Taro-Hayashi/On-the-15/acrylic-case/fully-acrylic/img/IMG_9139.jpeg

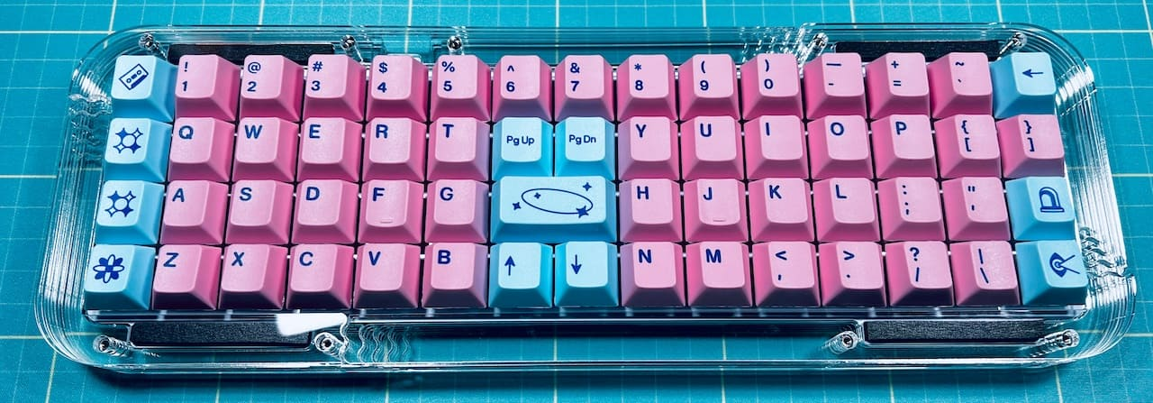
acrylic-case/fully-acrylic/img/IMG_9139.jpeg
