Taro-Hayashi/On-the-15/acrylic-case/fully-acrylic/img/onthe15c.jpg

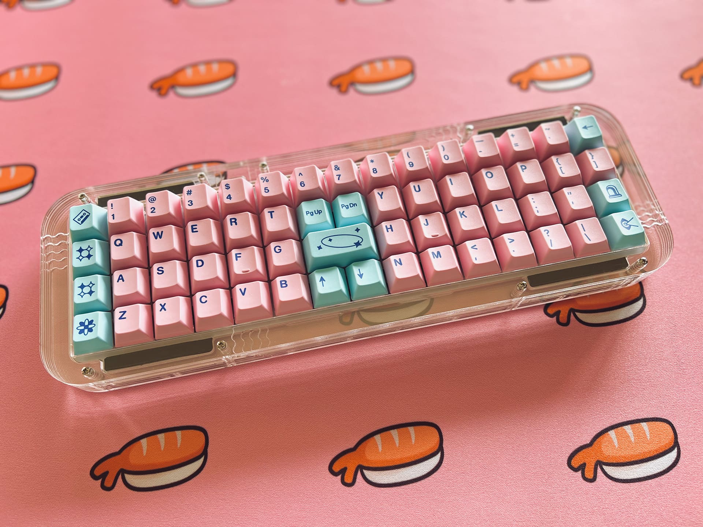
acrylic-case/fully-acrylic/img/onthe15c.jpg
