Taro-Hayashi/On-the-15/img/case1.png

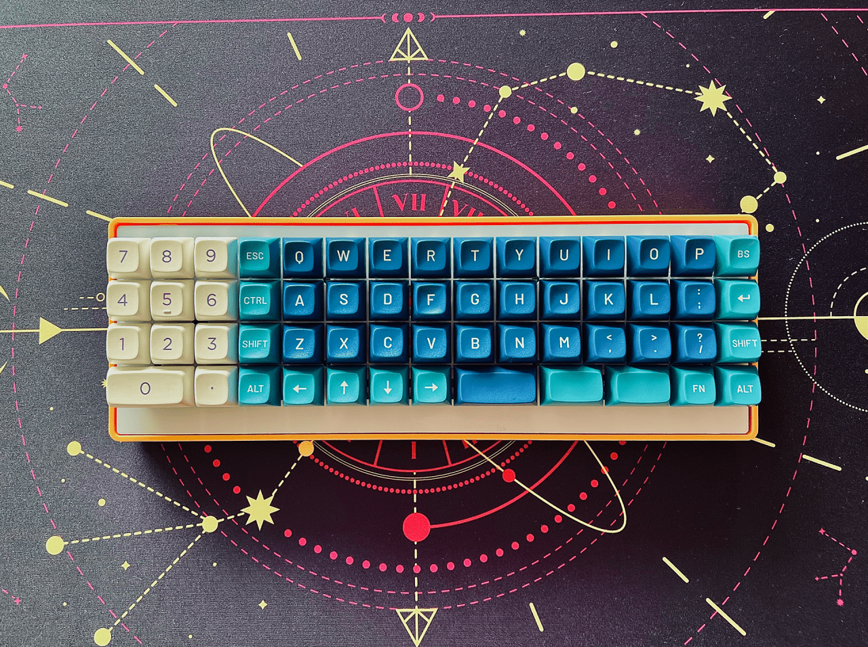
img/case1.png
