Taro-Hayashi/On-the-15/img/case2.png

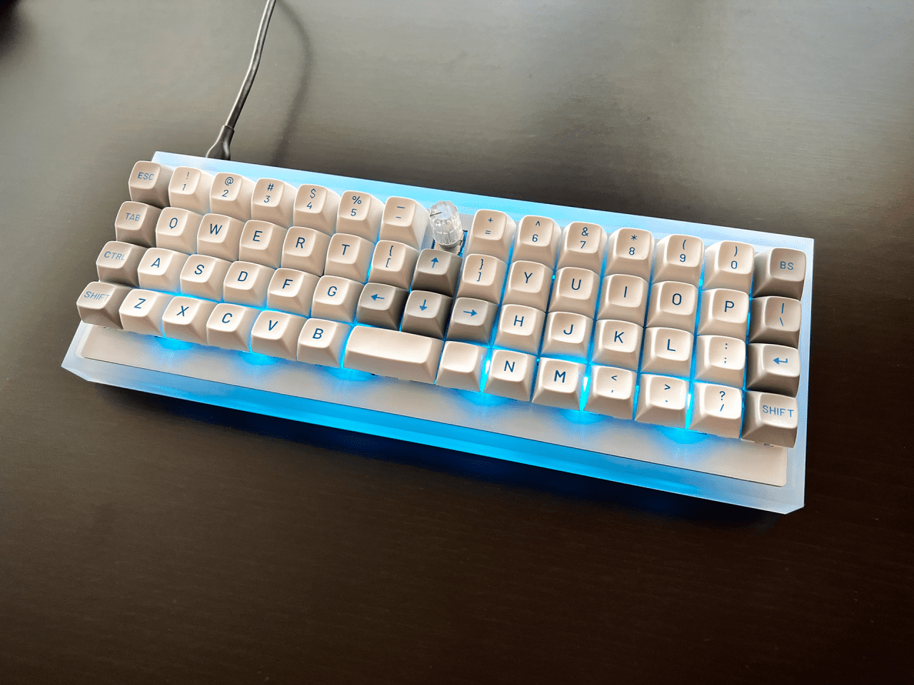
img/case2.png
