Taro-Hayashi/On-the-15/img/IMG_6119.jpg

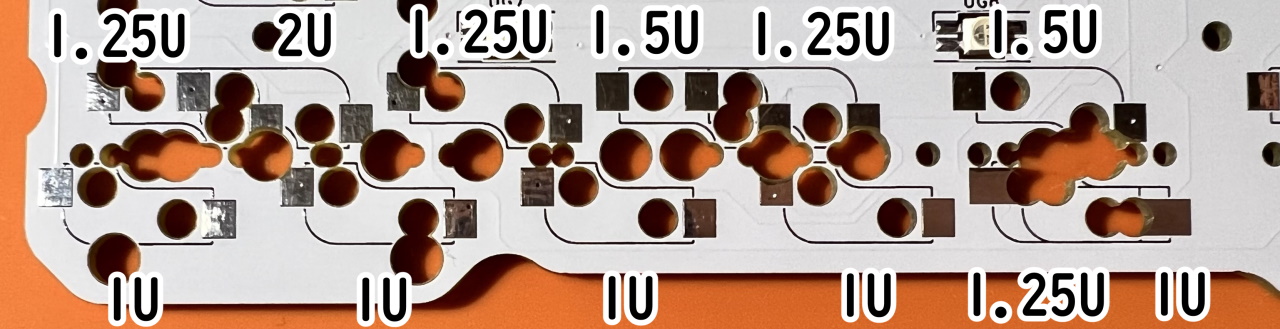
img/IMG_6119.jpg
