Taro-Hayashi/On-the-15/img/IMG_6120.jpg

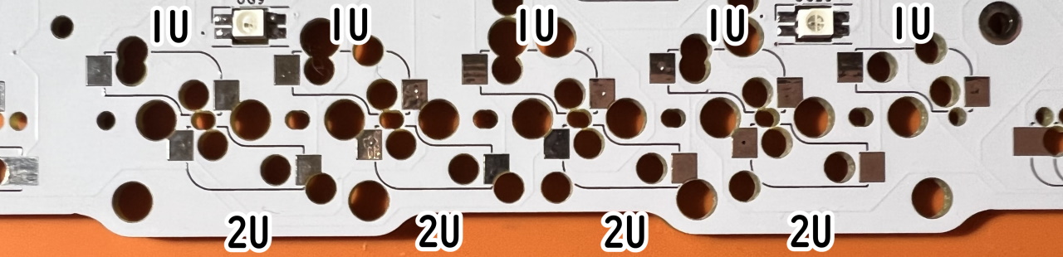
img/IMG_6120.jpg
