Taro-Hayashi/On-the-15/img/IMG_6123.jpg

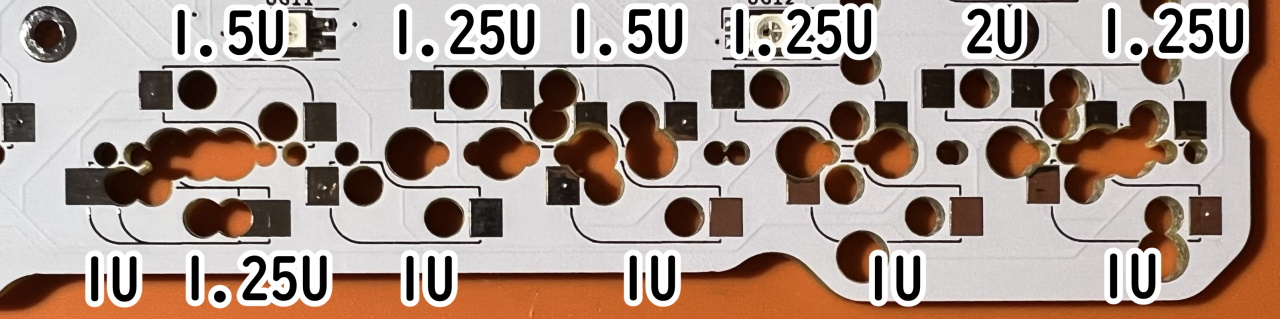
img/IMG_6123.jpg
