Taro-Hayashi/On-the-15/img/IMG_6135.JPEG

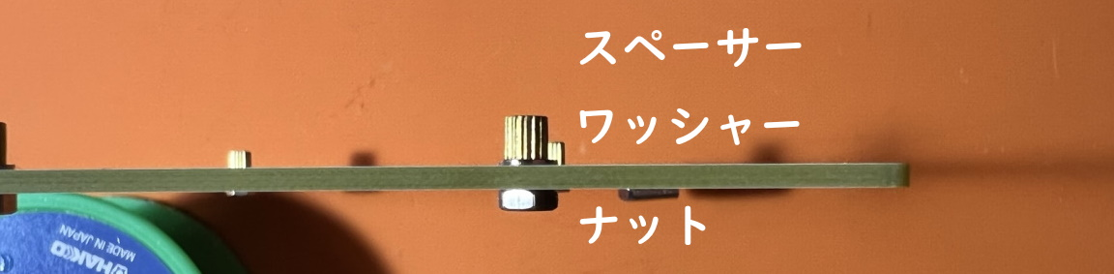
img/IMG_6135.JPEG
