Taro-Hayashi/On-the-15/img/IMG_6159.JPEG

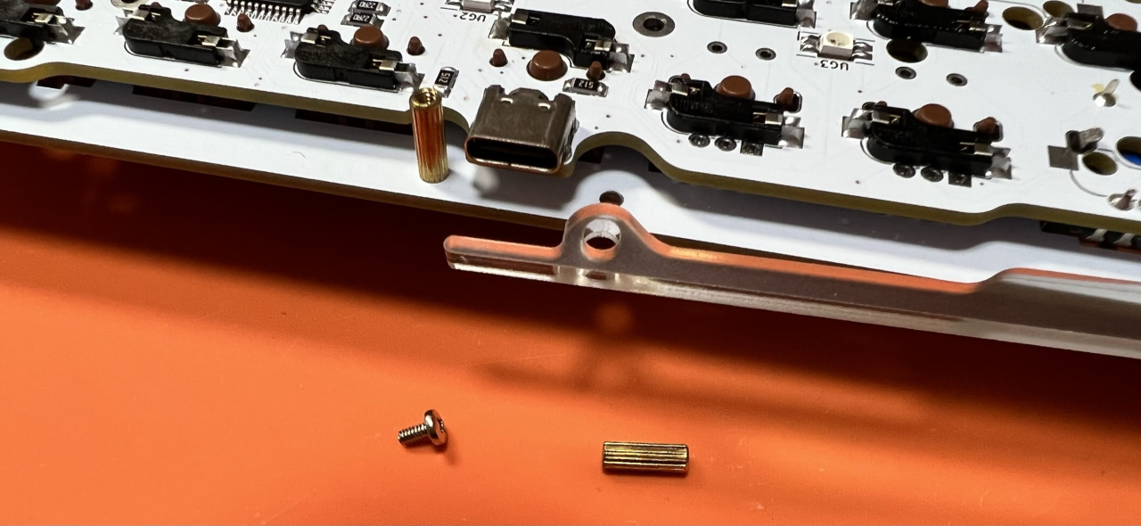
img/IMG_6159.JPEG
