Taro-Hayashi/On-the-15/img/IMG_6162.JPEG

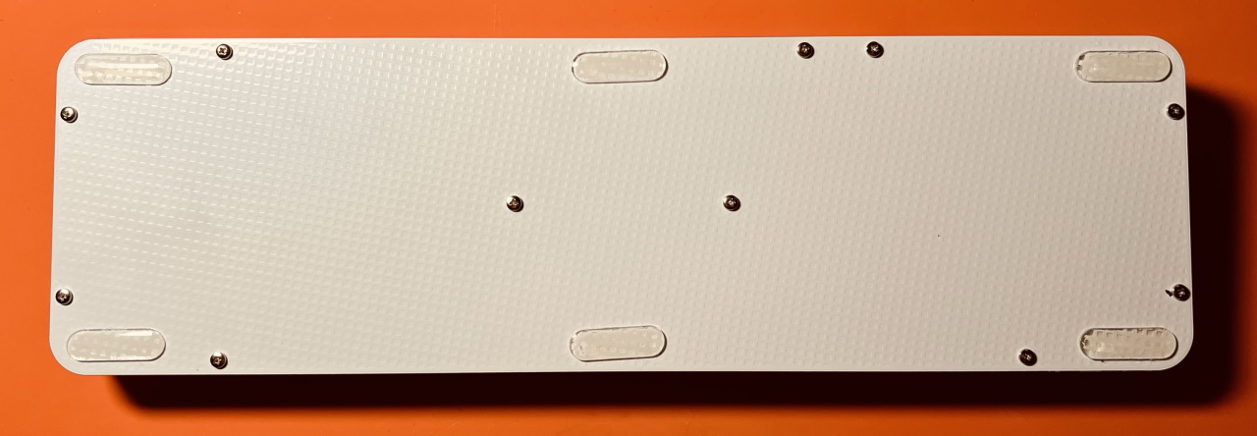
img/IMG_6162.JPEG
