Taro-Hayashi/On-the-15/img/IMG_6163.JPEG

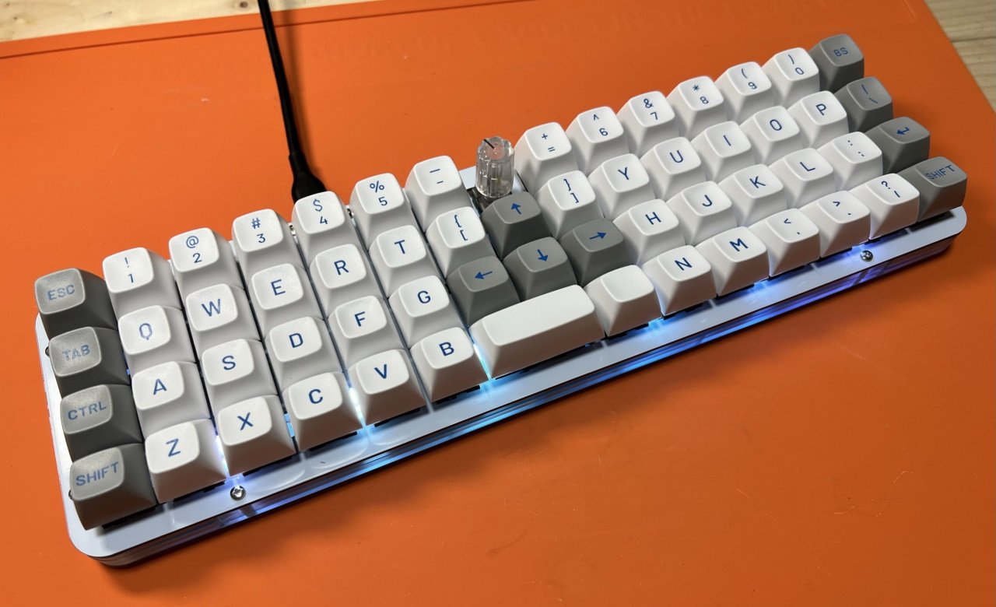
img/IMG_6163.JPEG
