Taro-Hayashi/On-the-15/img/IMG_6304.jpg

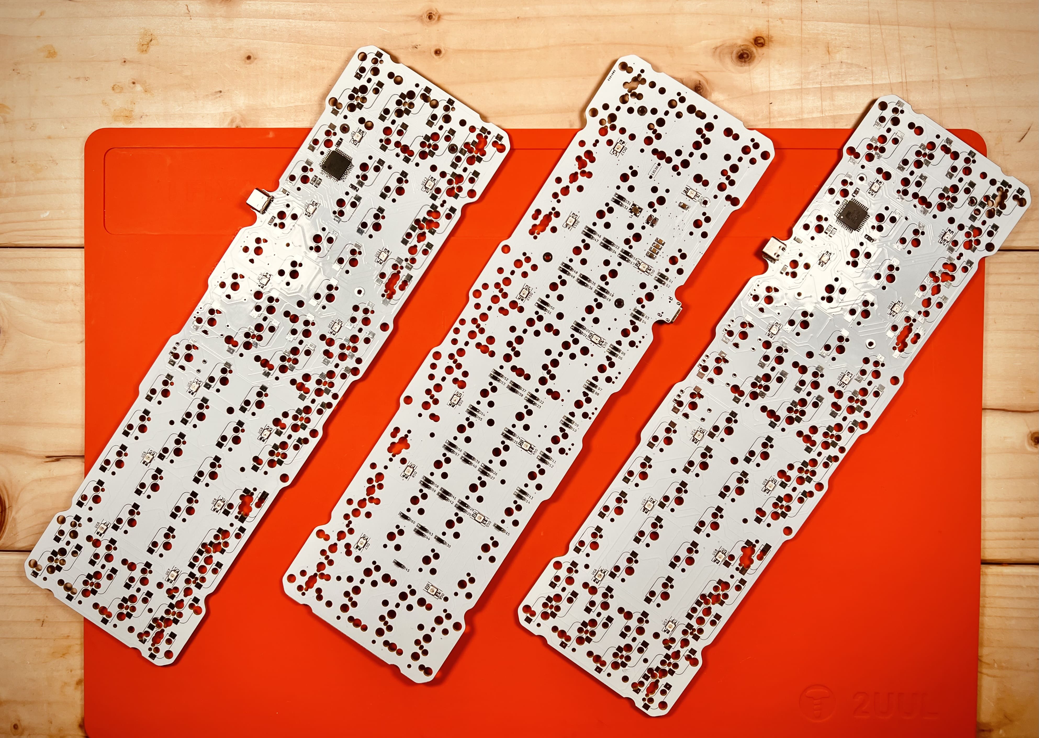
img/IMG_6304.jpg
