Taro-Hayashi/On-the-15/img/IMG_6330.jpg

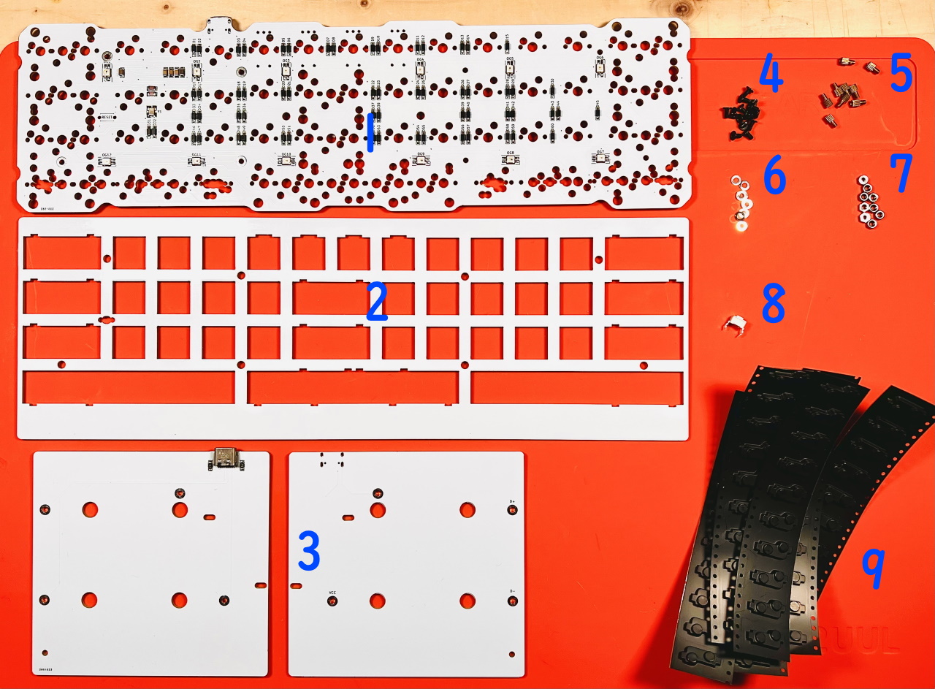
img/IMG_6330.jpg
