Taro-Hayashi/On-the-15/img/IMG_8033.jpg

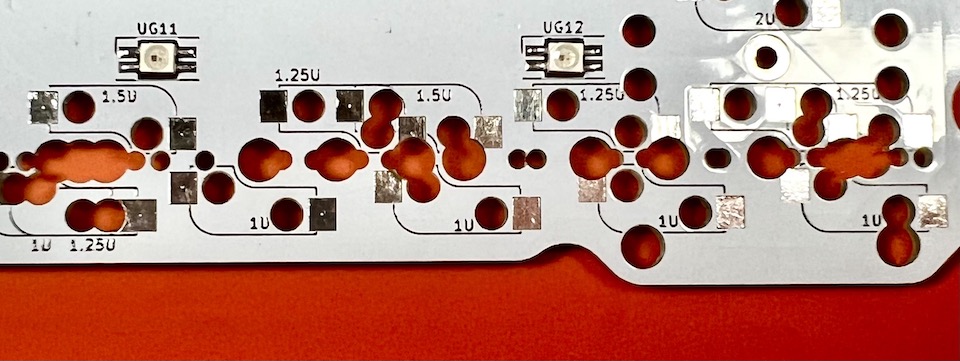
img/IMG_8033.jpg
