Taro-Hayashi/On-the-15/img/json.png

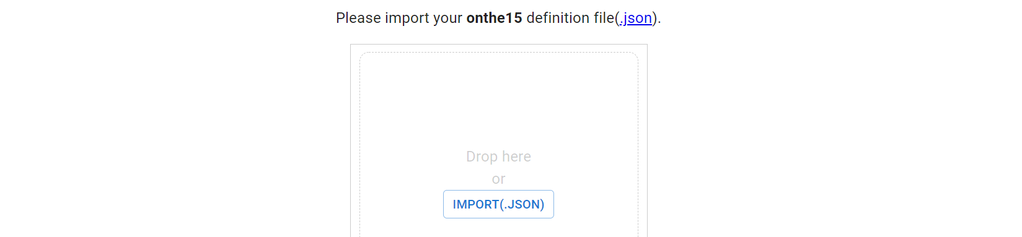
img/json.png
