Taro-Hayashi/On-the-15/img/keymaps.png

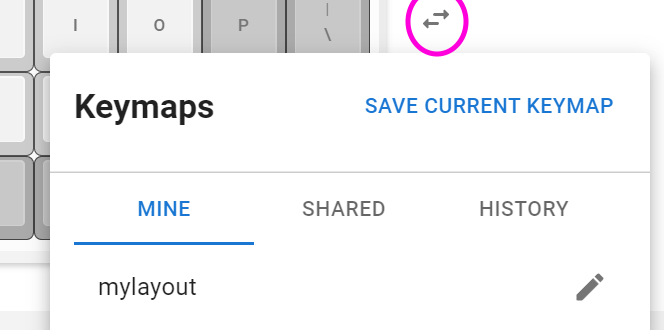
img/keymaps.png
