Taro-Hayashi/On-the-15/img/layoutoption.png

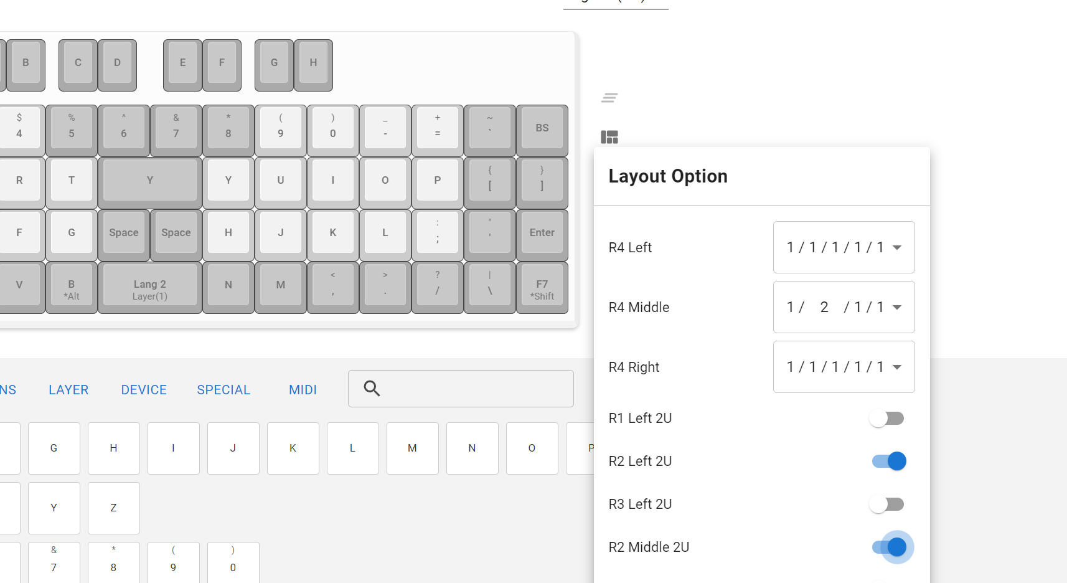
img/layoutoption.png
