Taro-Hayashi/On-the-15/img/remap07.png

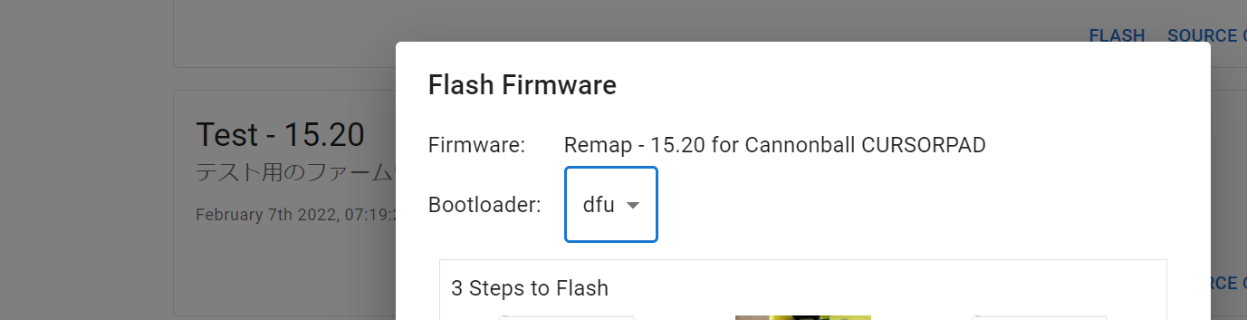
img/remap07.png
